thingSoC/TSOC_NEOLED/TSOC_NEOLED/eagleUp/eagleUp_TSOC_NEOLED_board_top.jpg

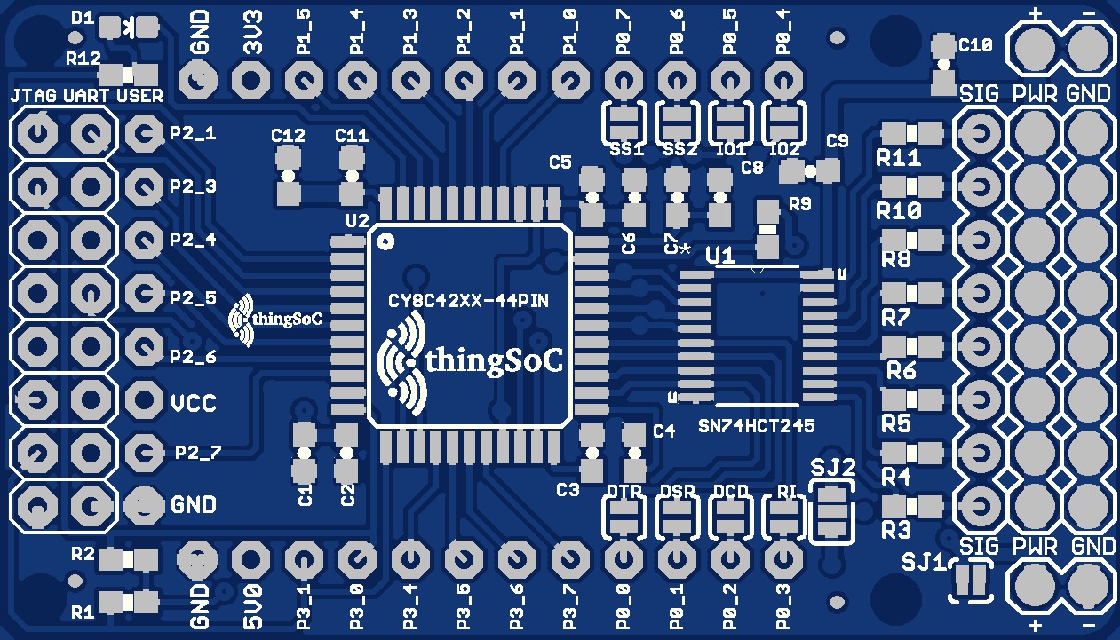
TSOC_NEOLED/eagleUp/eagleUp_TSOC_NEOLED_board_top.jpg
