thingSoC/TSOC_NEOLED/TSOC_NEOLED/images/product/TSOC_NEOLED_rails.png

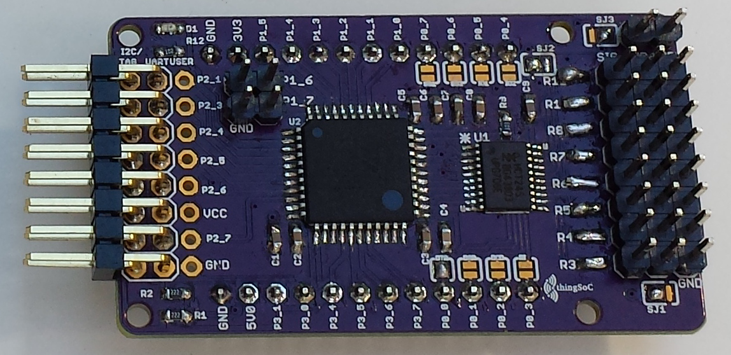
TSOC_NEOLED/images/product/TSOC_NEOLED_rails.png
