thingSoC/TSOC_NEOLED/TSOC_NEOLED/images/rev2.0/TSOC_NEOLED_bot.png

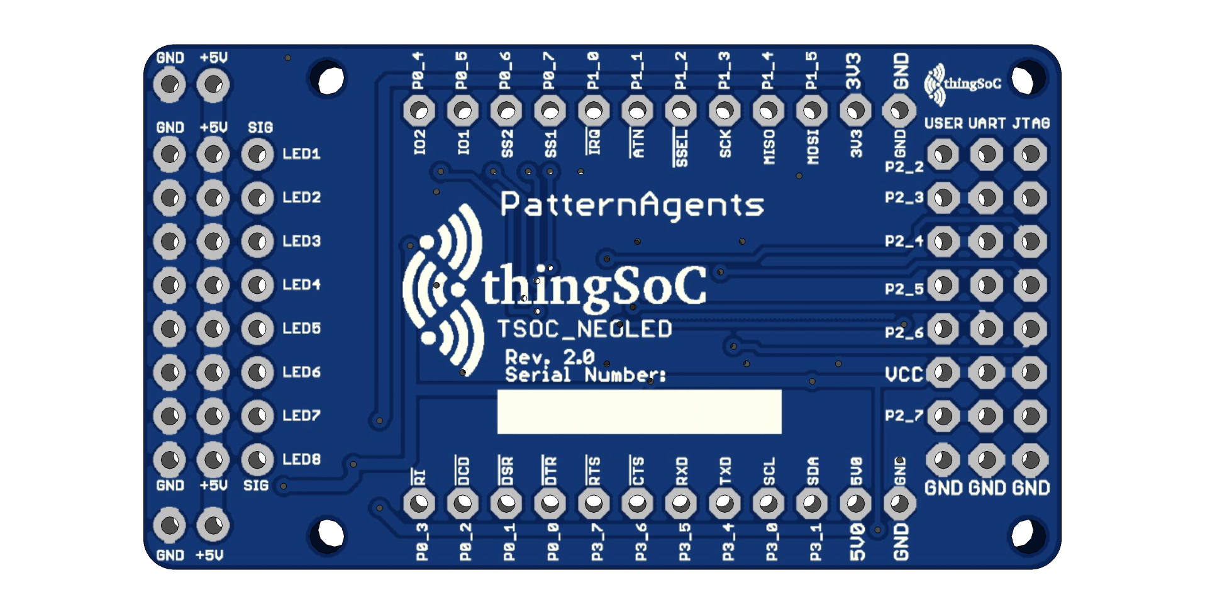
TSOC_NEOLED/images/rev2.0/TSOC_NEOLED_bot.png
