thingSoC/TSOC_NEOLED/TSOC_NEOLED/revisions/rev1.1/TSOC_NEOLED_sch.pdf

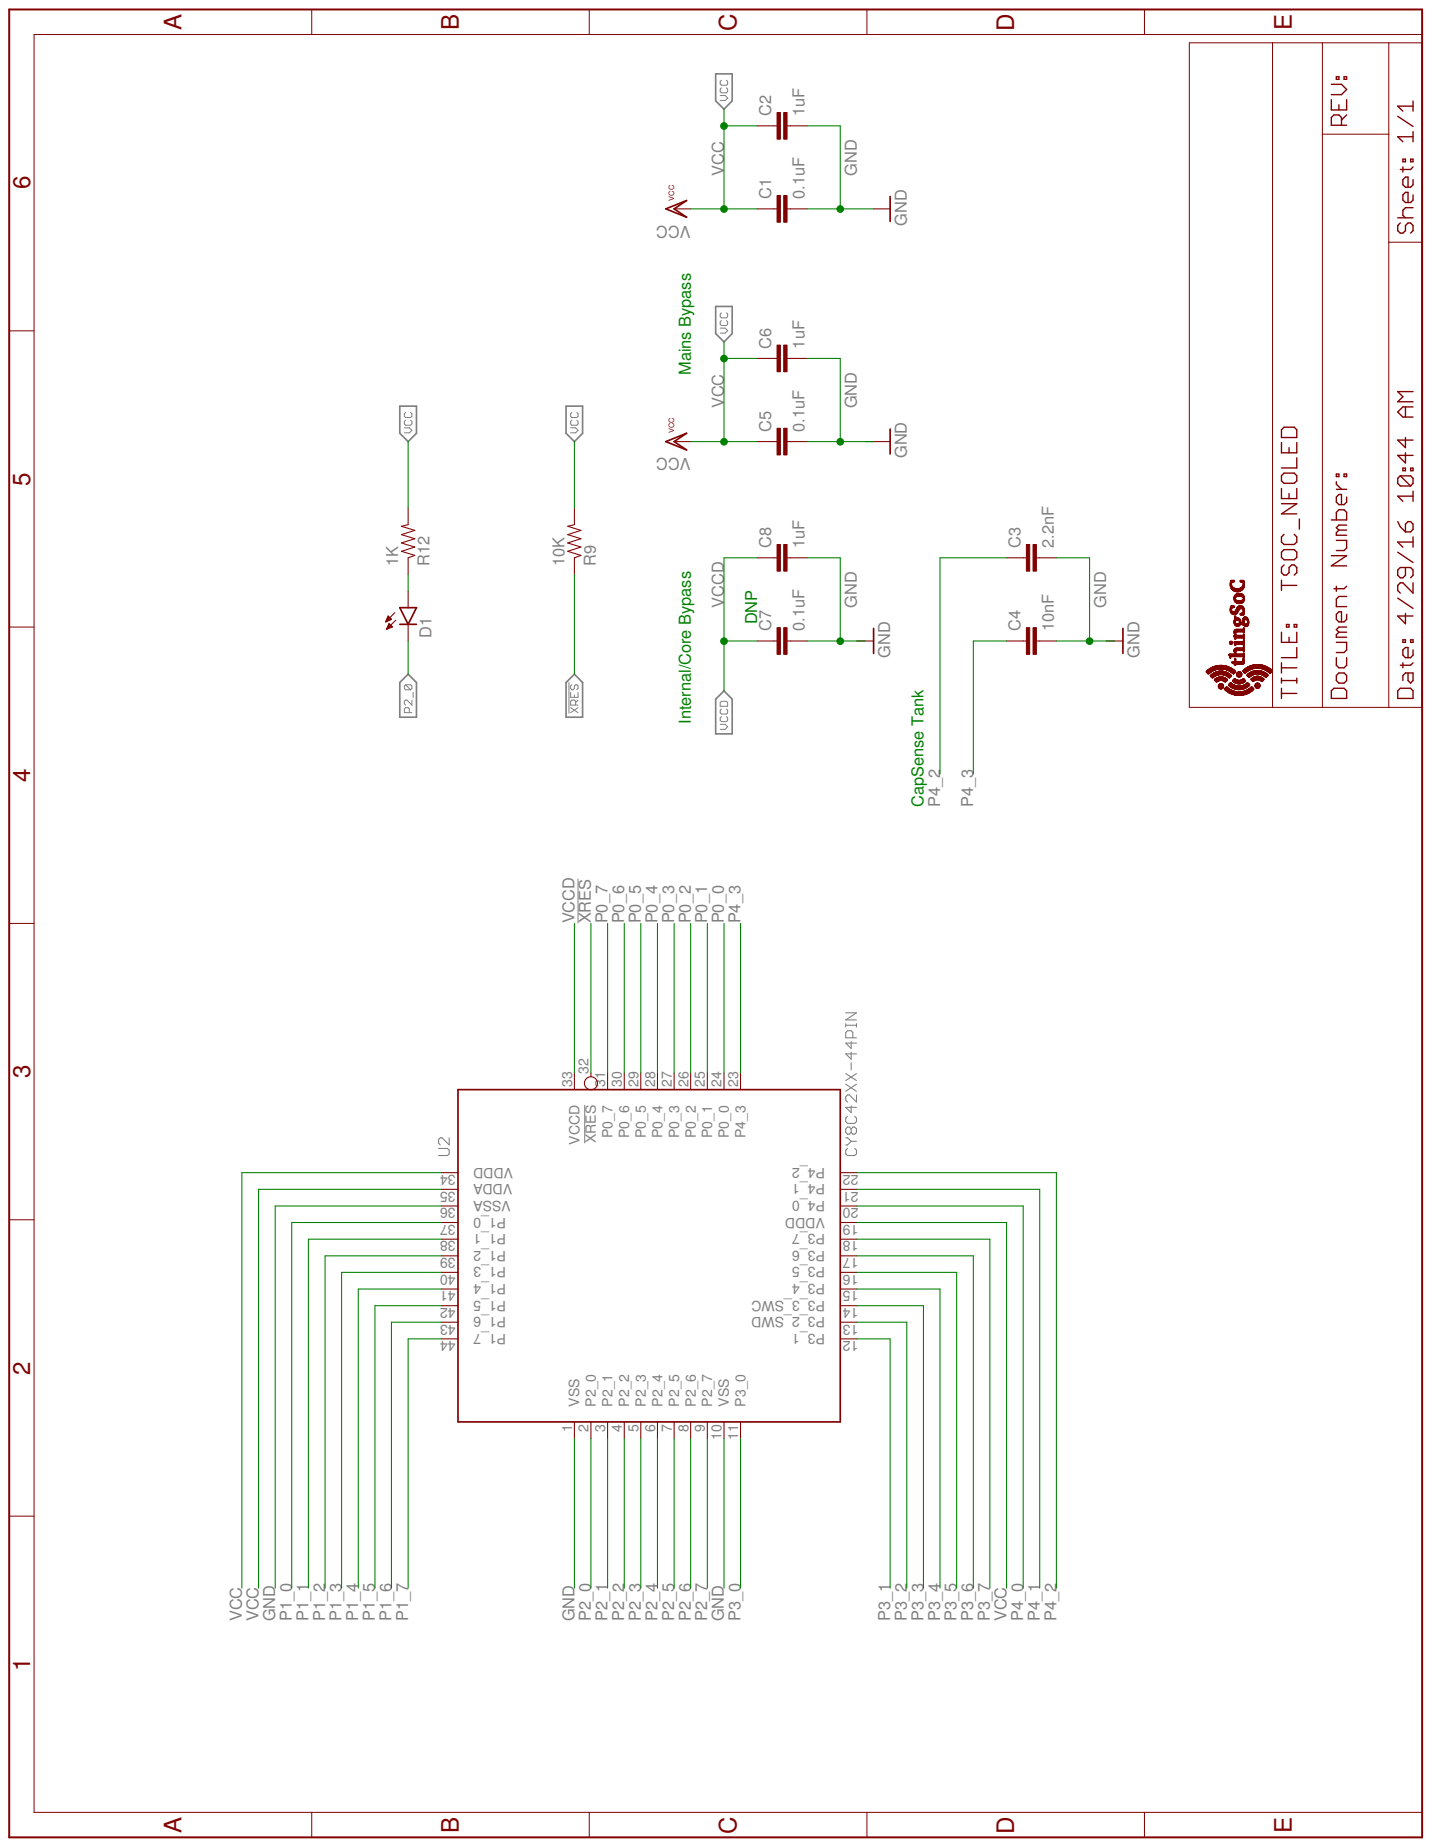
[picture p51: page 1]

TSOC-PCB-PLUS SN74HC245PW GND GND 0.1uF 1uF 0.1uF 1uF 0.1uF 1uF GND GND GND 0.1uF CCV CCV GND M02 GND 10K 10nF 2.2nF GND 1K M02 M02 2K2 2K2 ATN 6B RI 1C DCD 2C DSR 3C DTR 4C TXD 8C IO2 1B IO1 2B RTS 5C CTS 6C IRQ 5B SS2 3B SS1 4B CS 7B MOSI 10B MISO 9B SCK 8B GND 12C AGND 12B 3V3 11B RXD 7C SDA 10C SCL 9C 5V0 11C JDBG 1E JTDO 2E JRST 3E JTCK 4E JTMS 5E VTARG 6E JTDI 7E GNDJ 8E VCC 20 DIR 1 ~OE 19 A1 2 A2 3 A3 4 A4 5 A5 6 A6 7 A7 8 A8 9 GND 10 B1 18 B2 17 B3 16 B4 15 B5 14 B6 13 B7 12 B8 11 U1 R11 R10 R8 R7 R6 R5 R4 R3 VSS 1 P2_0 2 P2_1 3 P2_3 5 P2_4 6 P2_5 7 P2_7 9 VSS 10 P3_0 11 1_3P 21 D WS_2_3P 31 C WS_3_3P 41 4_3P 51 5_3P 61 7_3P 81 DDDV 91 0_4P 02 1_4P 12 2_4P 22 P4_3 23 P0_0 24 P0_1 25 P0_3 27 P0_4 28 P0_5 29 P0_7 31 XRES 32 VCCD 33 DDDV 43 ADDV 53 ASSV 63 0_1P 73 1_1P 83 3_1P 04 4_1P 14 5_1P 24 6_1P 34 7_1P 44 P2_2 4 P2_6 8 6_3P 71 P0_6 30 2_1P 93 P0_2 26 C1 C2 C5 C6 C7 C8 C9 J2 12345678 J4 12345678 J3 12345678 SJ1 SJ3 5V 12 J1 1 2 3 4 5 6 7 8 9 10 11 12 13 14 15 16 SJ2 RI DCD DSR DTR SS2 SS1 IO2 IO1 R9 C4 C3 R12 D1 SP2 21 SP1 21 2 R1 R GND GND GND GND GND GND GND VCC VCC VCC VCC VCC P1_2 P1_7 P1_6 P1_5 P1_4 P1_3 P1_1 P1_0 P2_0 P2_1 P2_2 P2_3 P2_4 P2_5 P2_6 P2_7 P3_0 P3_1 P3_2 P3_3 P3_4 P3_5 P3_6 P3_7 P4_0 P4_1 P4_2 P4_2 P4_3 P4_3 P0_0 P0_1 P0_2 P0_3 P0_4 P0_5 P0_6 P0_7 XRES VCCD VCCD ABCDE ABCDE 1 2 3 4 5 6 ABCDE ABCDE 1 2 3 4 5 6 ABCDE ABCDE 1 2 3 4 5 6 ABCDE ABCDE 1 2 3 4 5 6 GND GND VCC VCC GND GND DNP Internal/Core Bypass Mains Bypass CapSense Tank

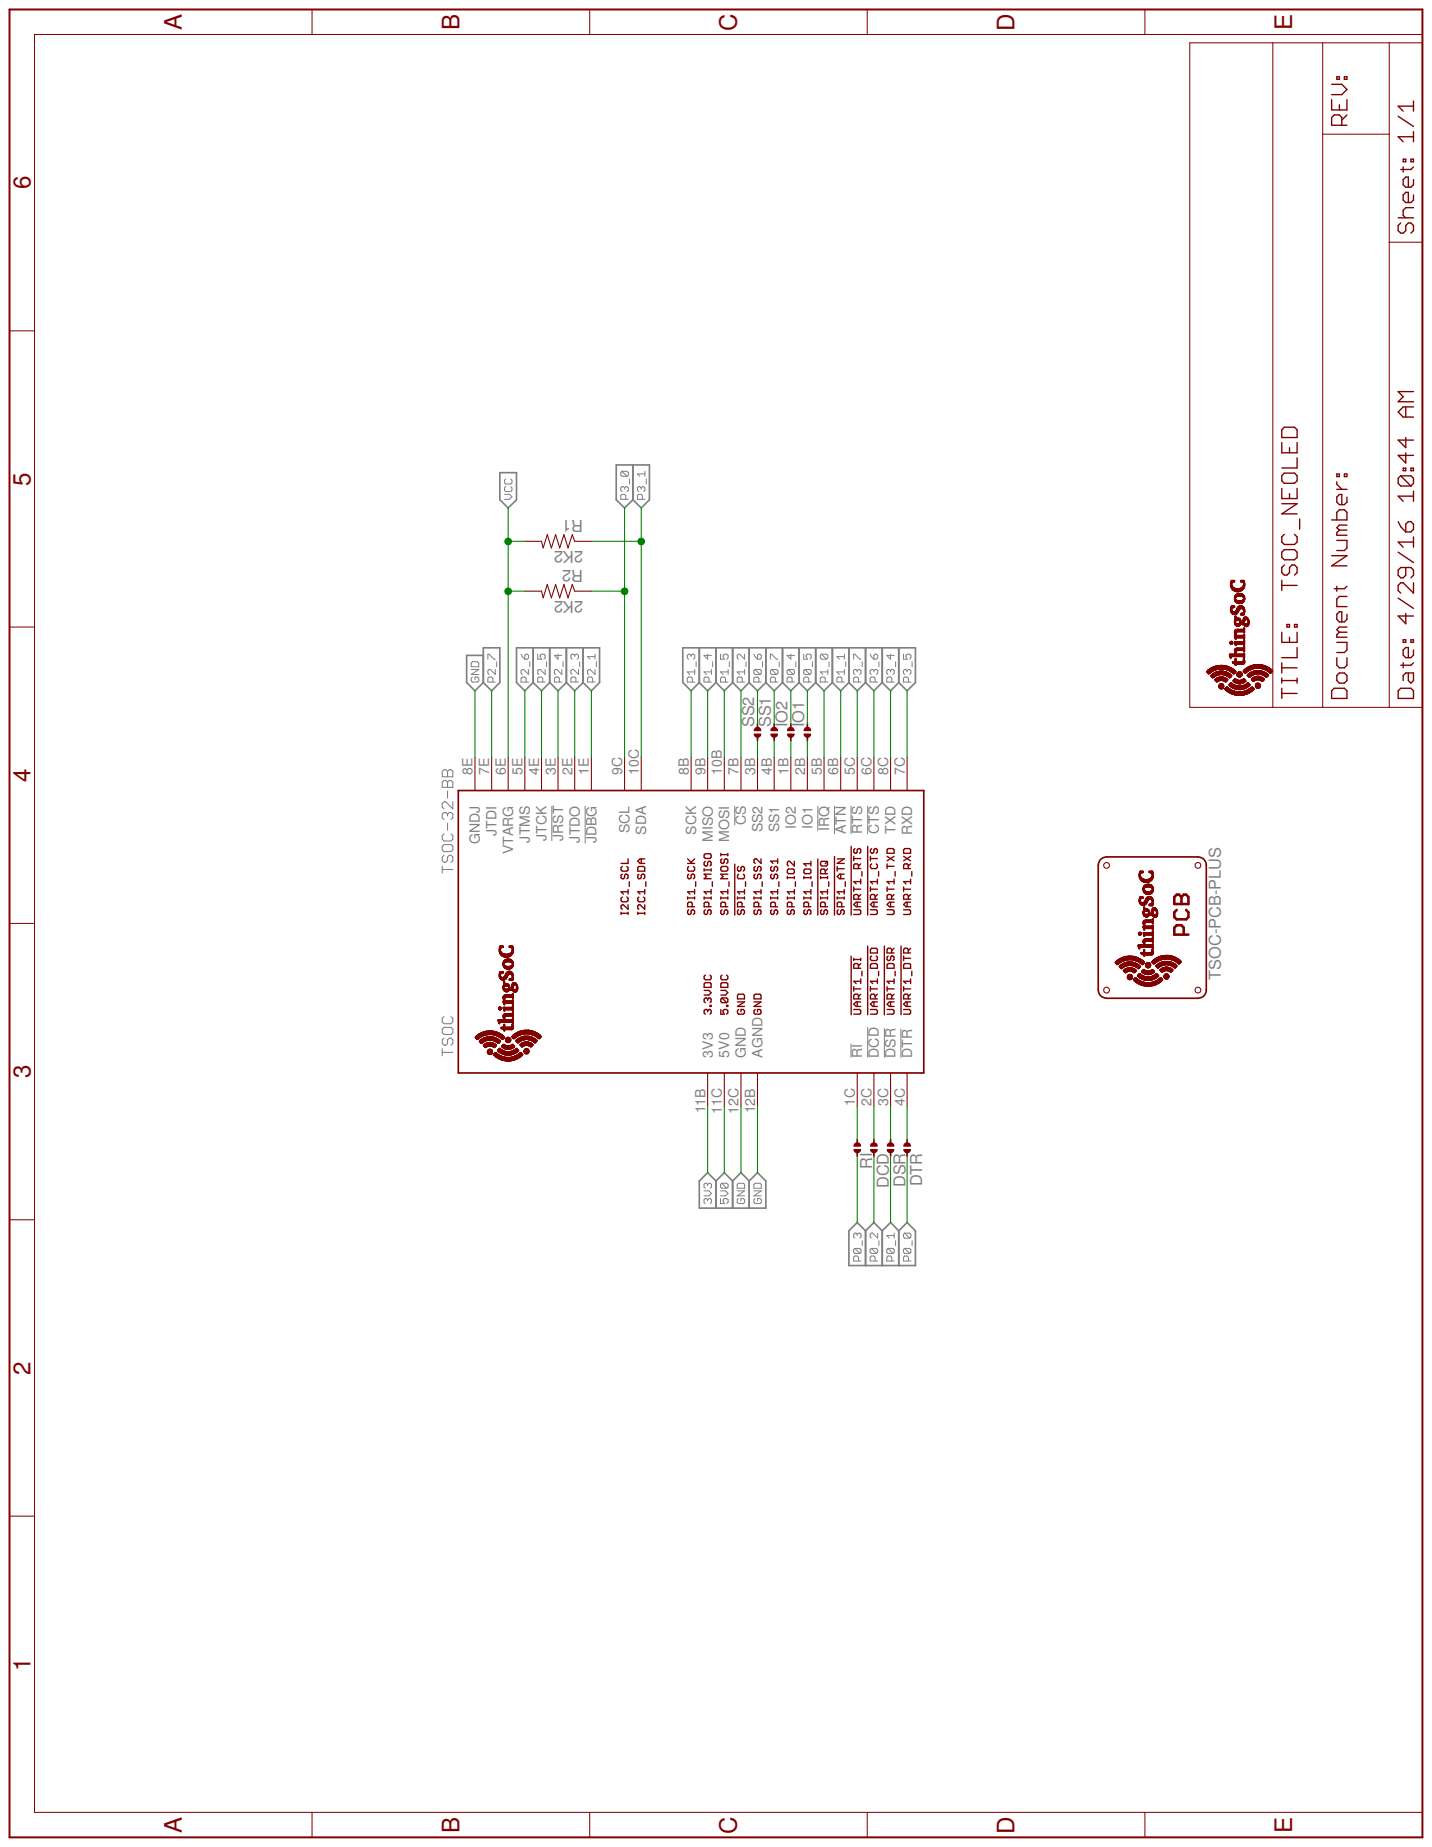
[picture p52: page 2]

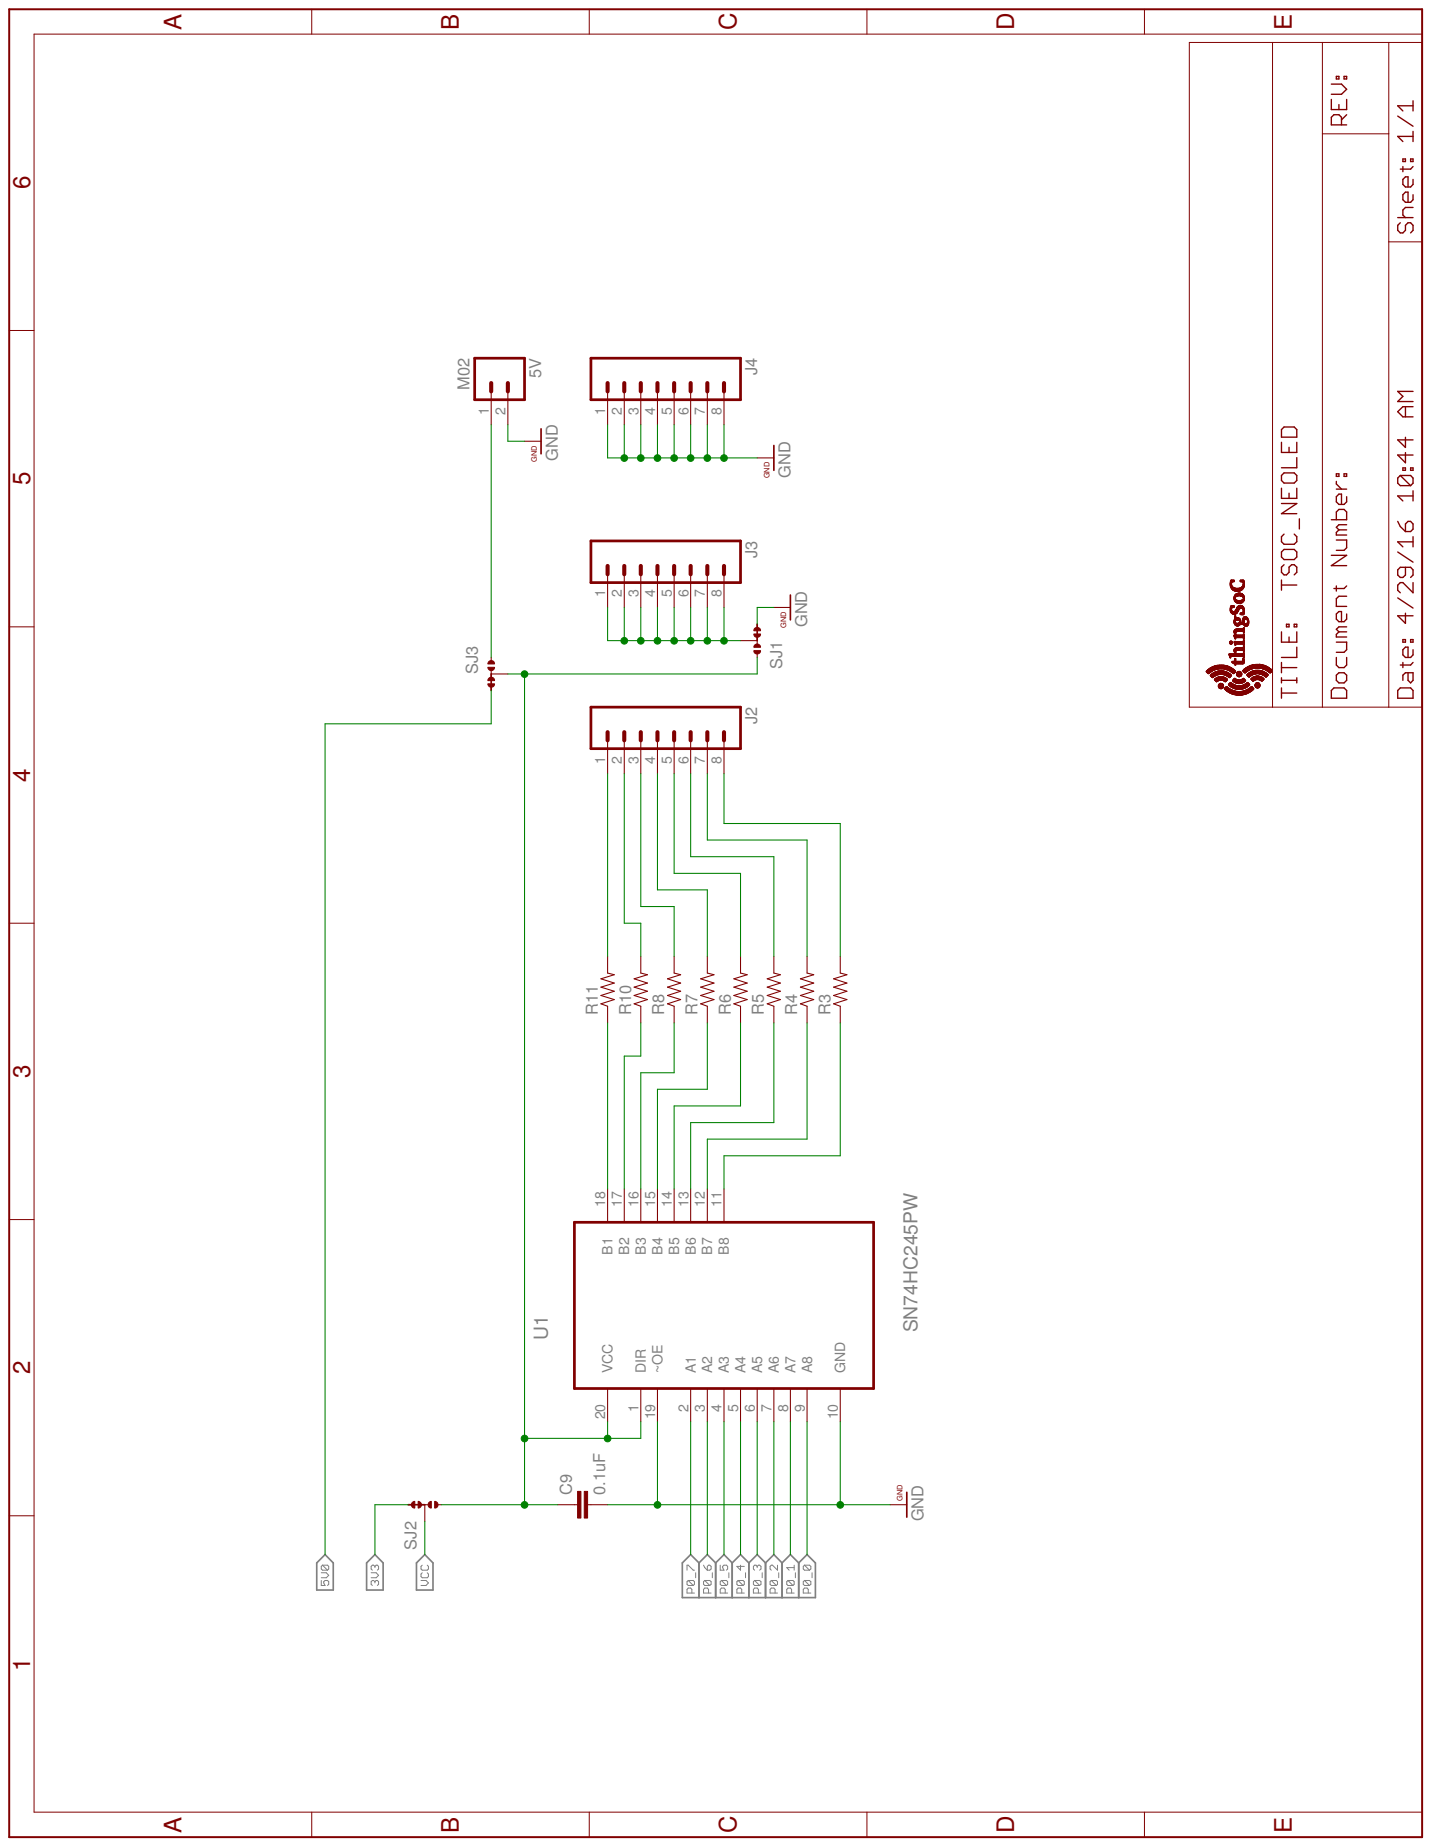
[picture p53: page 3]

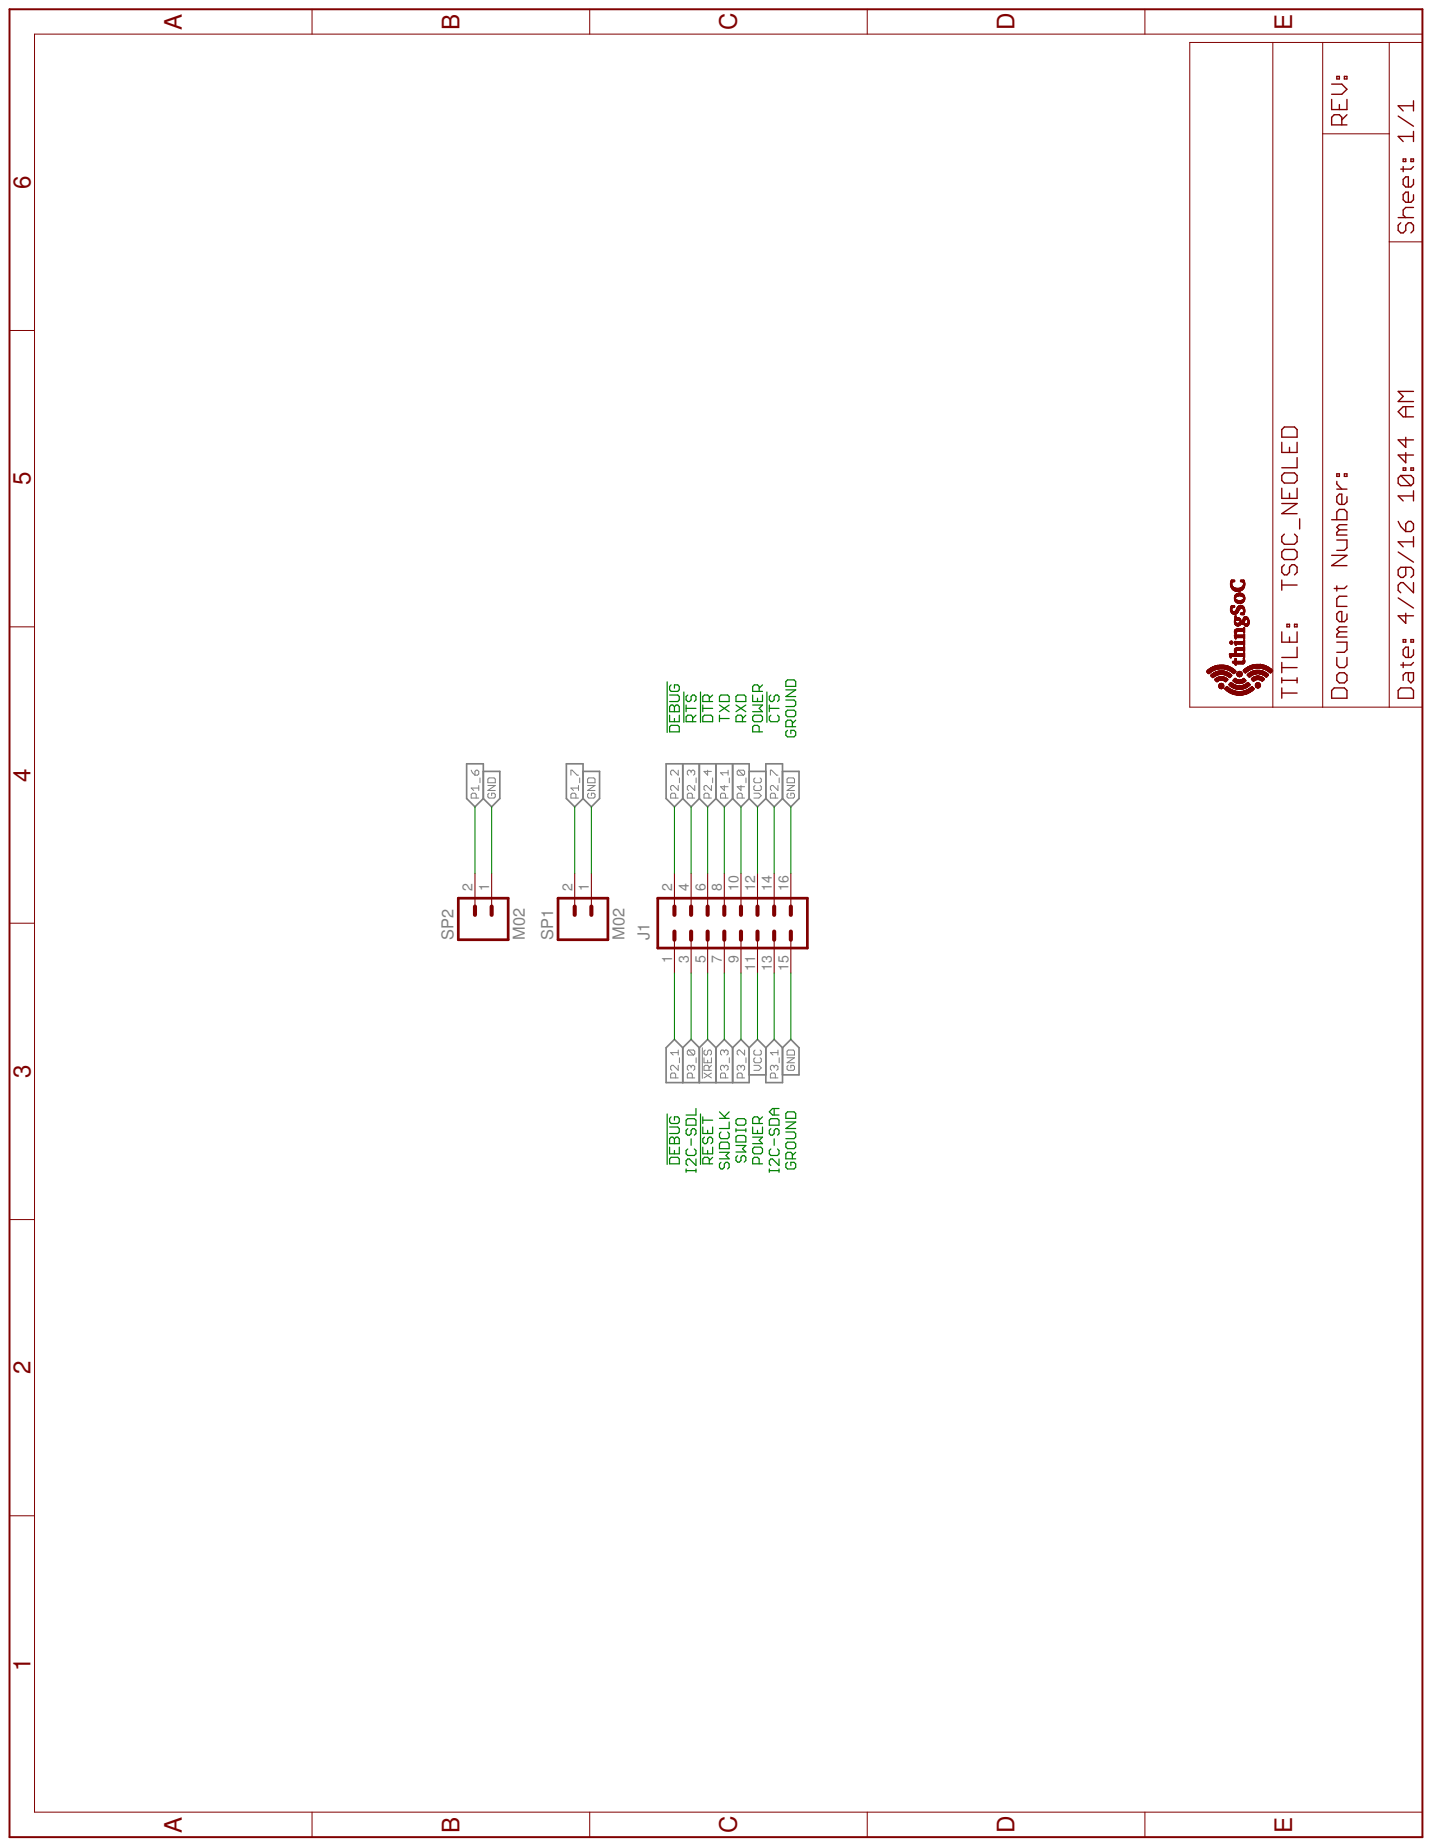
[picture p54: page 4]
