thingSoC/TSOC_NEOLED/TSOC_NEOLED/revisions/rev1.1/TSOC_NEOLED_brd.pdf

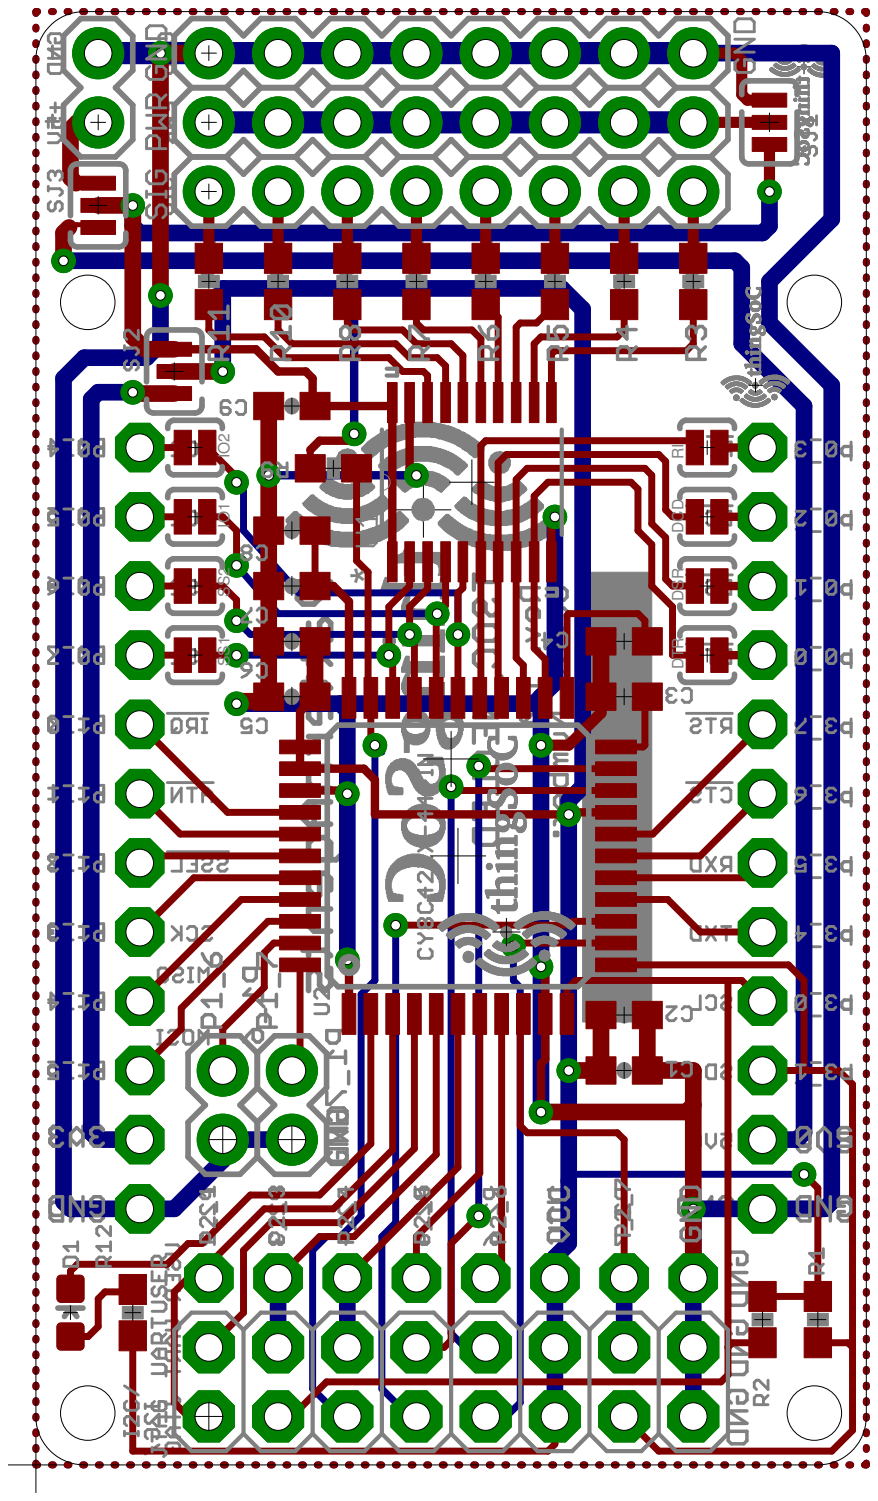
[picture p60: page 1]

* RI DCD DSR DTR SS2 SS1 IO2 IO1
