thingSoC/TSOC_NEOLED/TSOC_NEOLED/revisions/rev1.1/TSOC_NEOLED_bsilk.pdf

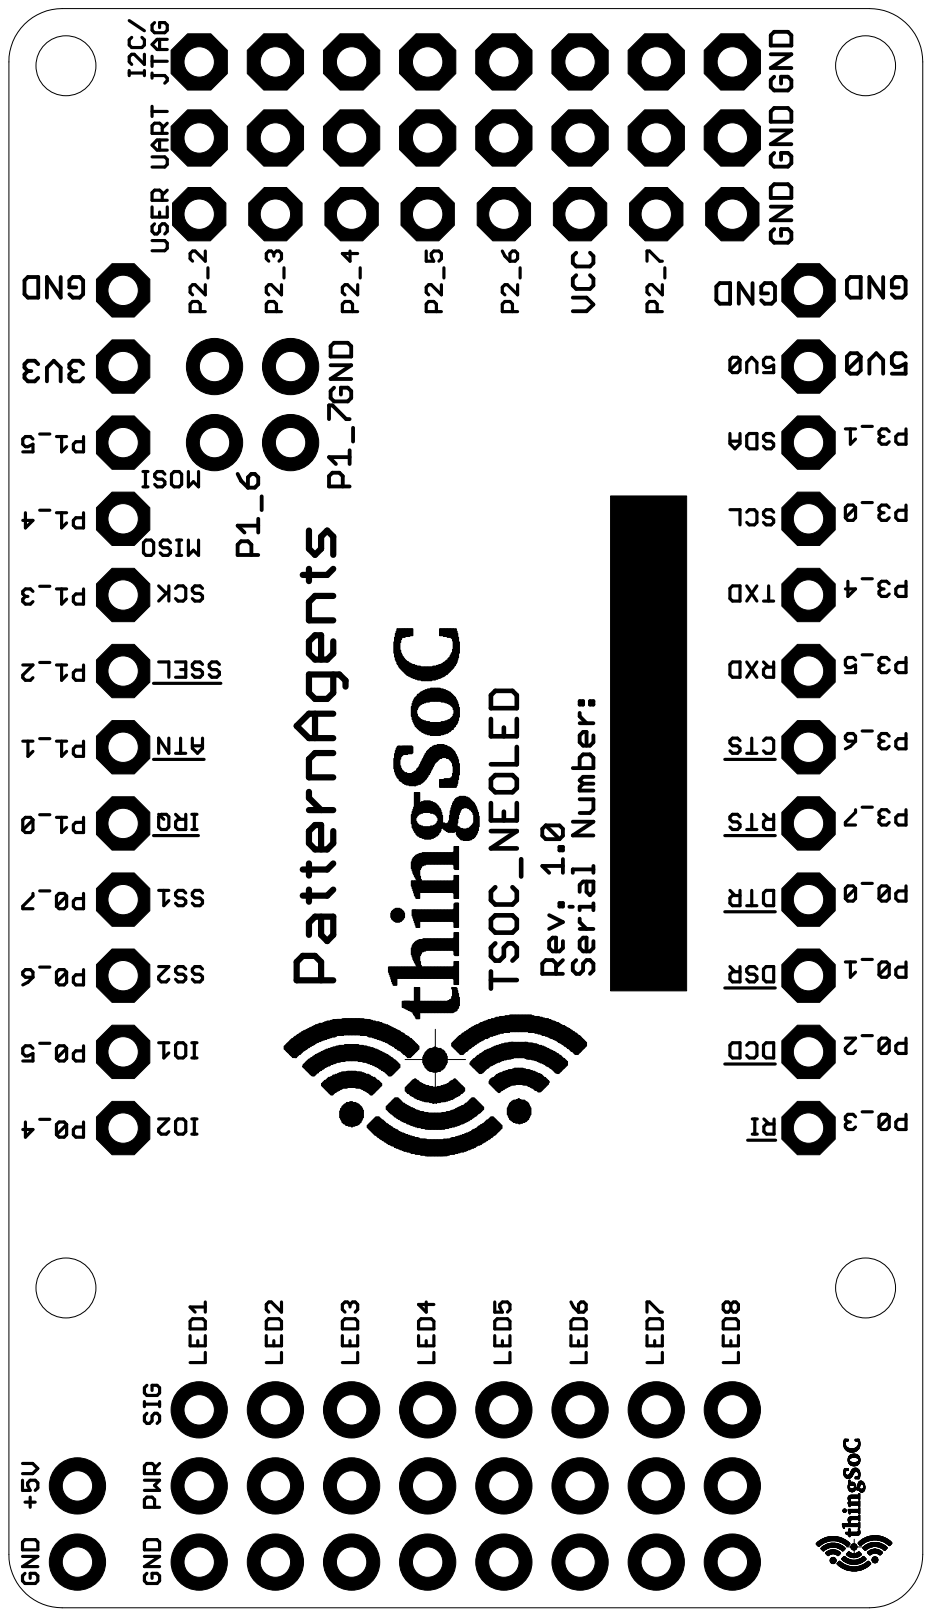
[picture p61: page 1]
